JoshuaEgwuatu/Capstone-Spring2023-CitizenAirQualitySensor/Documentation/Electrical/Schematics/ReadMe.md

A collection of all the schematics that are related to and used for the design and its subsystems.  Schematics may be PDF or JPEG format.
