JoshuaEgwuatu/Capstone-Spring2023-CitizenAirQualitySensor/Reports/Presentations/LithiumIonBatteries.pdf

# Lithium Ion Batteries

By Kaleb Irwin
Team 1

# Why batteries?

The world needs compact energy storage

Devices need electricity when not plugged in

Can be used as power backups

# Advantages of Li+

High Energy density

Low self discharge (under half NiCd and NiMH)

Minimal memory effect

Longer lifespan than other common compositions

# Individual cells

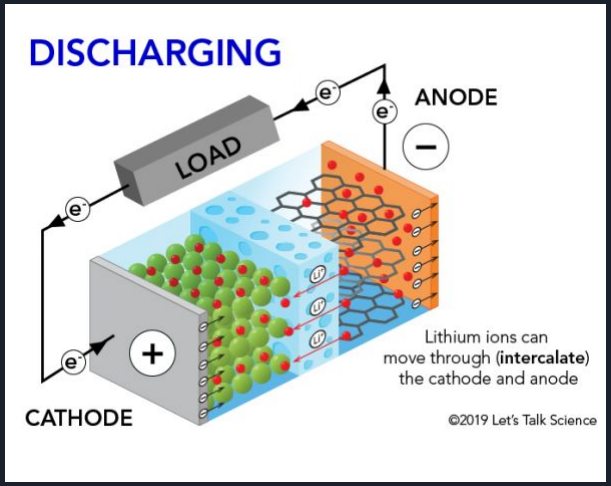
[picture p28: figure]

Consists of

- Cathode
- Anode
- Electrolyte

Materials for all of the components can be tweaked to alter the performance of the battery

# Cathode

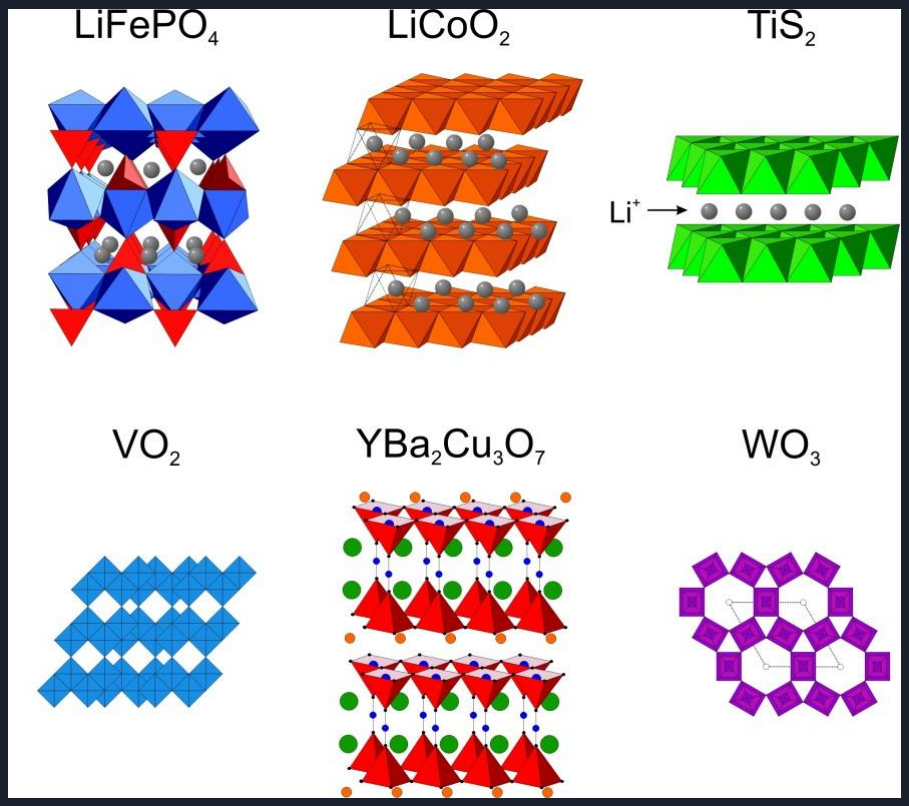
[picture p29: figure]

Positive Electrode

Household batteries mark the cathode with +

Typically a Metal Oxide Crystal with Lithium Metal inserted

Absorbs Electrons that are made by the battery

# Common Cathode Materials

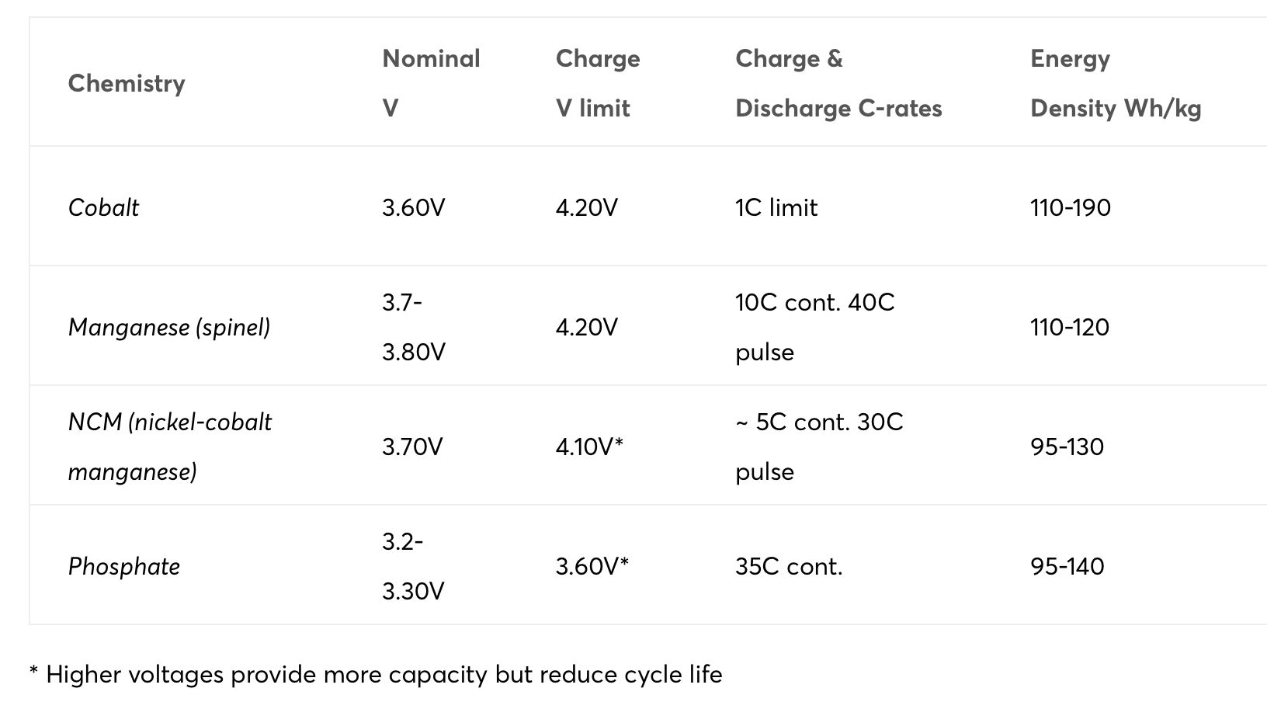
[picture p30: figure]

Different Cathode
materials can provide
- higher energy
densities
- higher current
output
- more charge
cycles

# Electrolyte

Chemical Separator

usually a lithium salt

Permeable for lithium ions but not electrons

Originally these were only permeable in one direction

Today they are bi-directional

# Common Electrolytes

Most common by far is Lithium Hexafluorophosphate

Other additives can be placed in solution with the salt to decrease the deposition rate or increase the reaction rate

Increasingly common is solid electrolytes that limit the degradation of the battery and are much safer.

# Anode

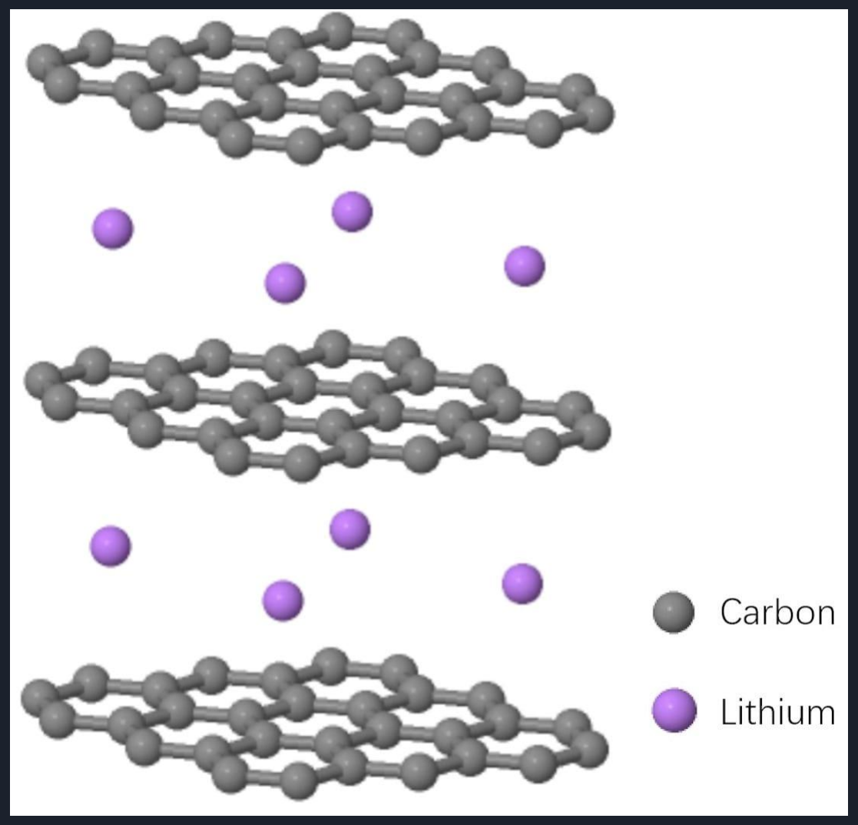
[picture p31: figure]

Negative Electrode

Emitter for the electrons generated

Almost always made of graphite due to its ability to place lithium ions between layers and its high conductivity

# Other Anodes

Graphite anodes require six carbon atoms per lithium ion

This is a waste of space and energy density

Silicon can be used as it binds to more lithium

- This is expensive and dangerous as it expands while discharging

Usually silicon is added to the graphite as an impurity of around 3% to increase energy density

Also use lithium titanate to decrease charge time

# Electrochemistry

Two reactions happen

The first one is a reaction at the anode

This generates an electron and a positively charged lithium ion and releases the chemical potential as electrical potential

# Electrochemistry

The second reaction happens at the cathode

The metal oxide and lithium ion react with the electron and form the multi metal oxide

# Electrochemistry

The reaction rate at the cathode is determined by the availability of electrons

Larger resistances in the external circuit that connects the cathode and anode limit how many electrons flow to the cathode

This means the discharge rate is determined by the resistance of the external circuit

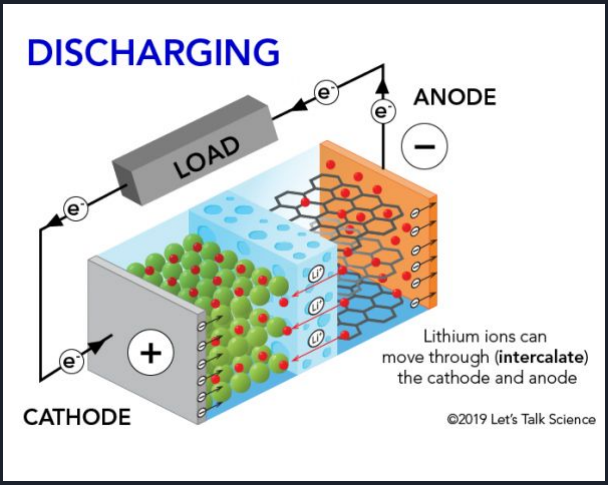
[picture p32: figure]

# What determines Voltage?

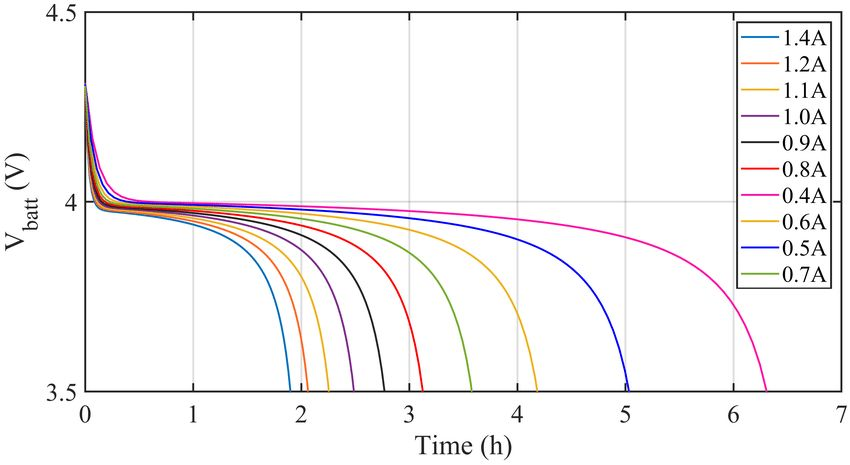
[picture p33: figure]

The voltage is intrinsic to the reaction and is based on the compounds used.

The voltage is slightly dependant on concentration

Because of this the voltage can change as the battery is
discharged

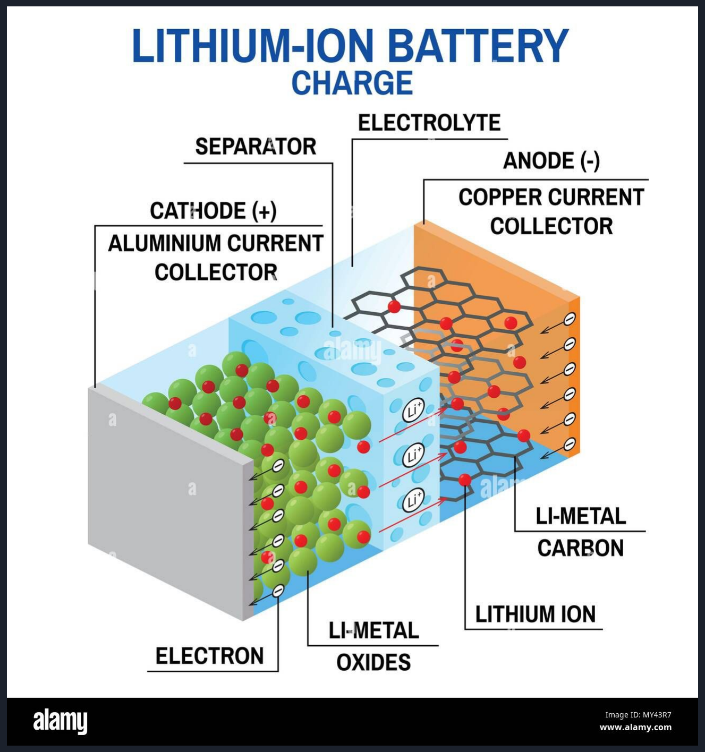
[picture p34: figure]

# Charging

A higher voltage than the
discharge voltage is applied

This supplies enough energy to cause the reactions to reverse

The electrons then leave the metal oxide and return to the graphite sheets

# Format of cells

Putting two cells in series will cause their voltages to add

Putting two cells in parallel will cause their capacities to add

Commonly abbreviated with S and P

Ex. 4s2p

Allows operation at higher voltages and load requirements

More efficient than one big battery

# Charging Multi-Celled batteries

Requires 3 steps

Constant current charging

Voltage balancing so all the cells are the same voltage

Constant Voltage charging

# Lifetime performance

Lifetime of the battery is determined by

- Temperature of the battery
- Reaction is exothermic so it heats the battery
- Reaction is 100% reversible
- Some of the lithium is deposited on the electrodes and is lost
- Charge and discharge current
- Increasing these also increases the rate of deposition

# References

https://www.energy.gov/science/doe-explainsbatteries

https://batteryuniversity.com/article/bu-204-how-do-lithium-batteries-work

https://www.targray.com/li-ion-battery/cathode-materials

https://en.wikipedia.org/wiki/Lithium-ion_battery
