JoshuaEgwuatu/Capstone-Spring2023-CitizenAirQualitySensor/Documentation/ProjectPhotos/Box1Exterior1.pdf

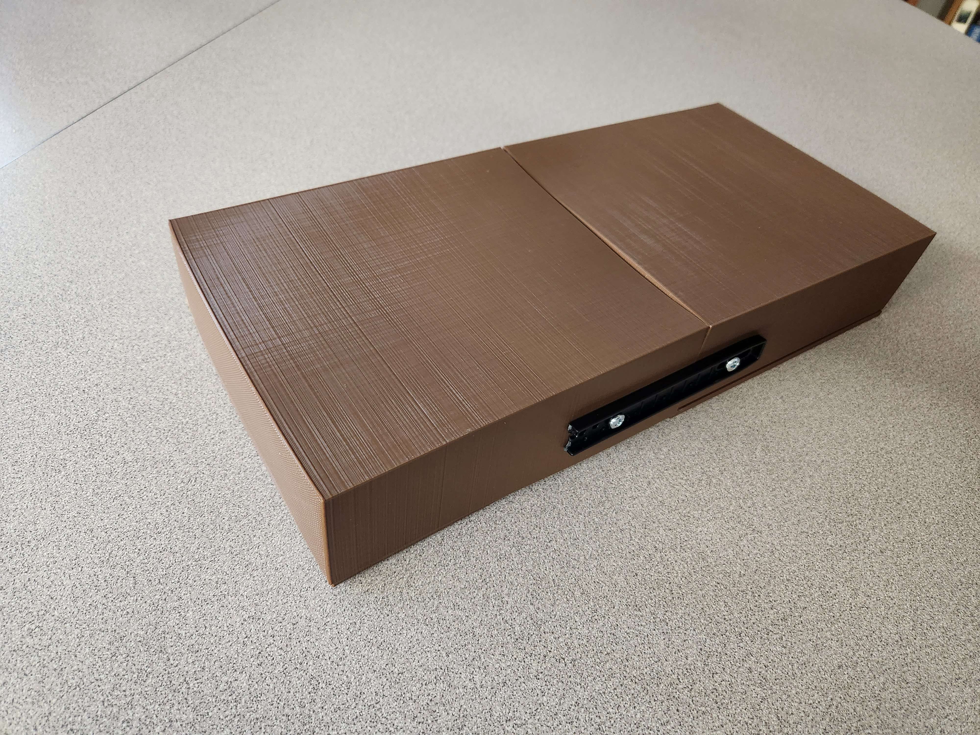
[picture p41: page 1]
