JoshuaEgwuatu/Capstone-Spring2023-CitizenAirQualitySensor/Documentation/ProjectPhotos/Box1Exterior2.pdf

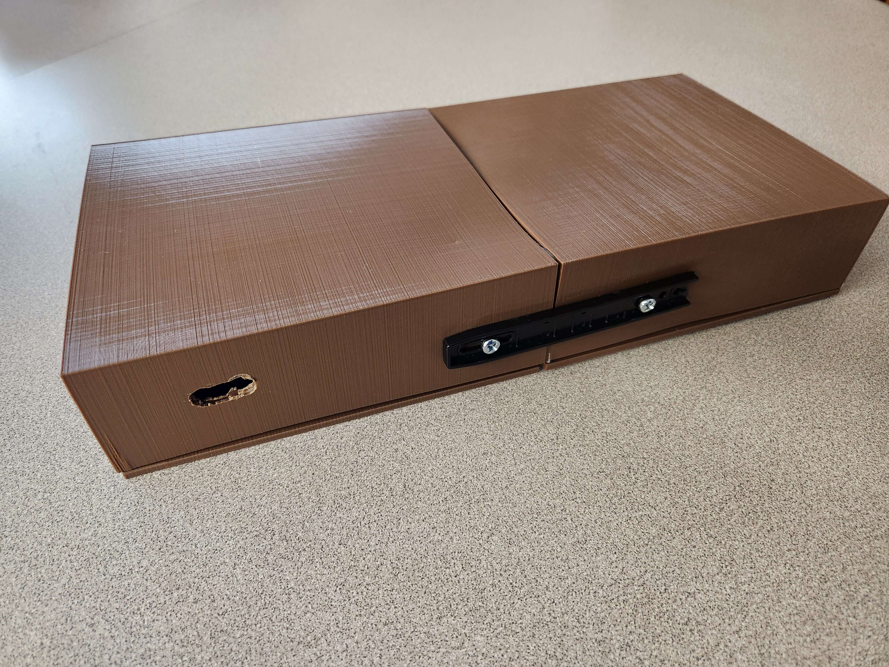
[picture p42: page 1]
