JoshuaEgwuatu/Capstone-Spring2023-CitizenAirQualitySensor/Documentation/ProjectPhotos/Box1Interior.pdf

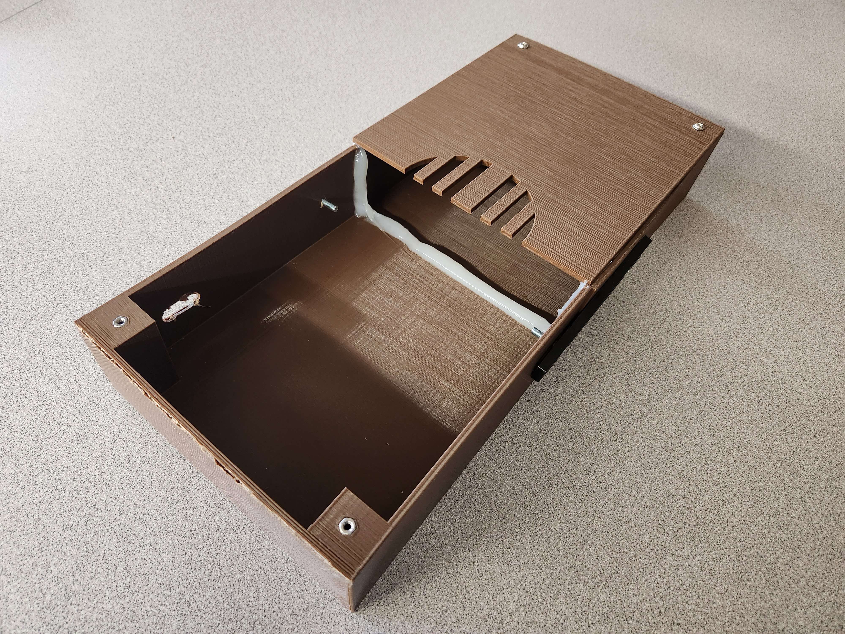
[picture p43: page 1]
