JoshuaEgwuatu/Capstone-Spring2023-CitizenAirQualitySensor/Documentation/ProjectPhotos/Box1Vent.pdf

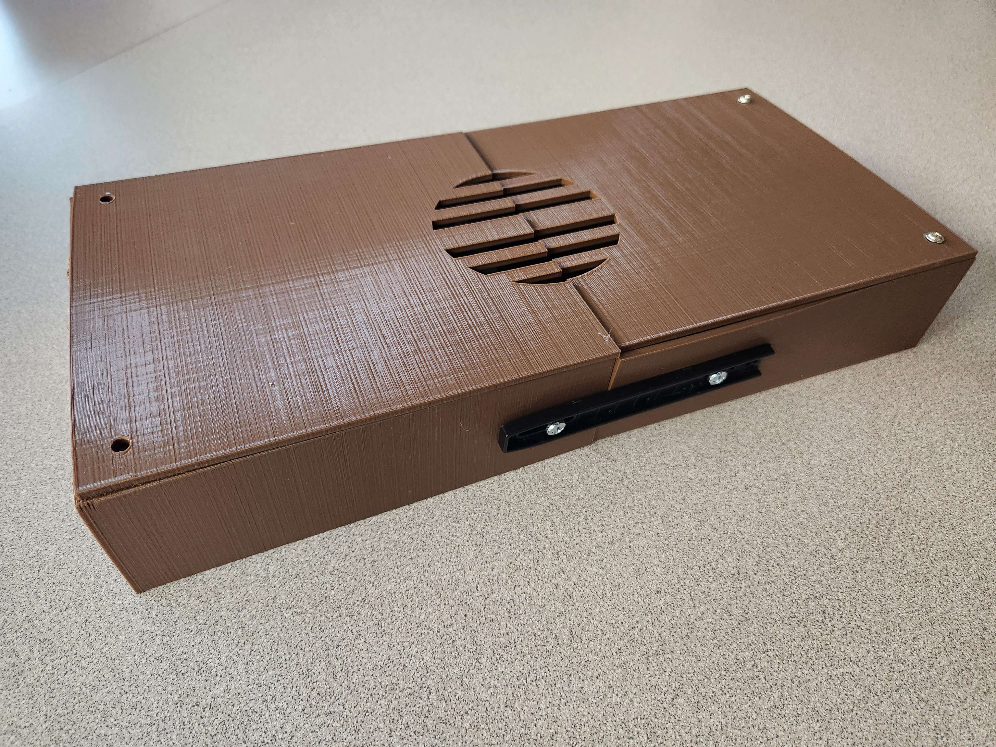
[picture p44: page 1]
