JoshuaEgwuatu/Capstone-Spring2023-CitizenAirQualitySensor/Documentation/ProjectPhotos/Box2Exterior.pdf

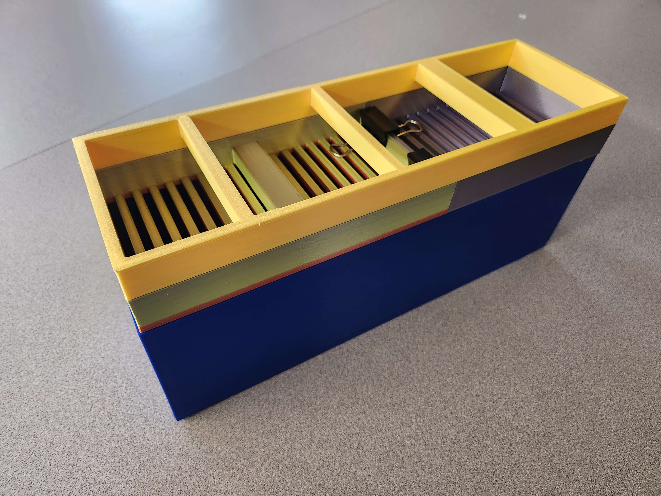
[picture p45: page 1]
