JoshuaEgwuatu/Capstone-Spring2023-CitizenAirQualitySensor/Documentation/ProjectPhotos/GUTS1.pdf

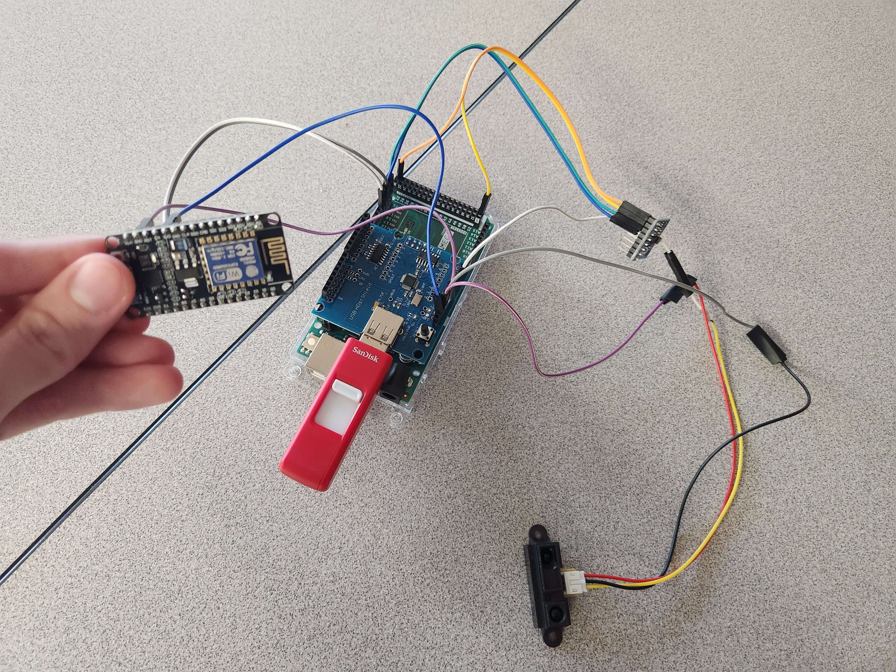
[picture p48: page 1]
