JoshuaEgwuatu/Capstone-Spring2023-CitizenAirQualitySensor/Documentation/ProjectPhotos/GUTS2.pdf

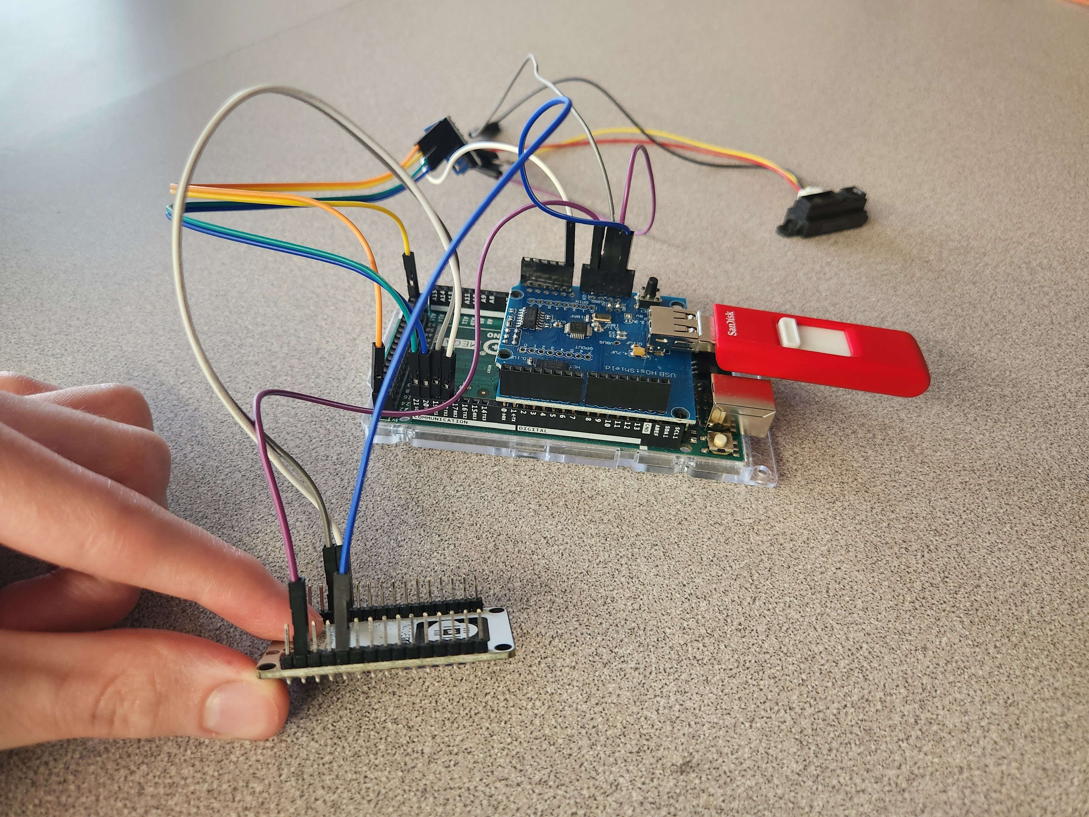
[picture p49: page 1]
