JoshuaEgwuatu/Capstone-Spring2023-CitizenAirQualitySensor/Documentation/ProjectPhotos/GUTS3.pdf

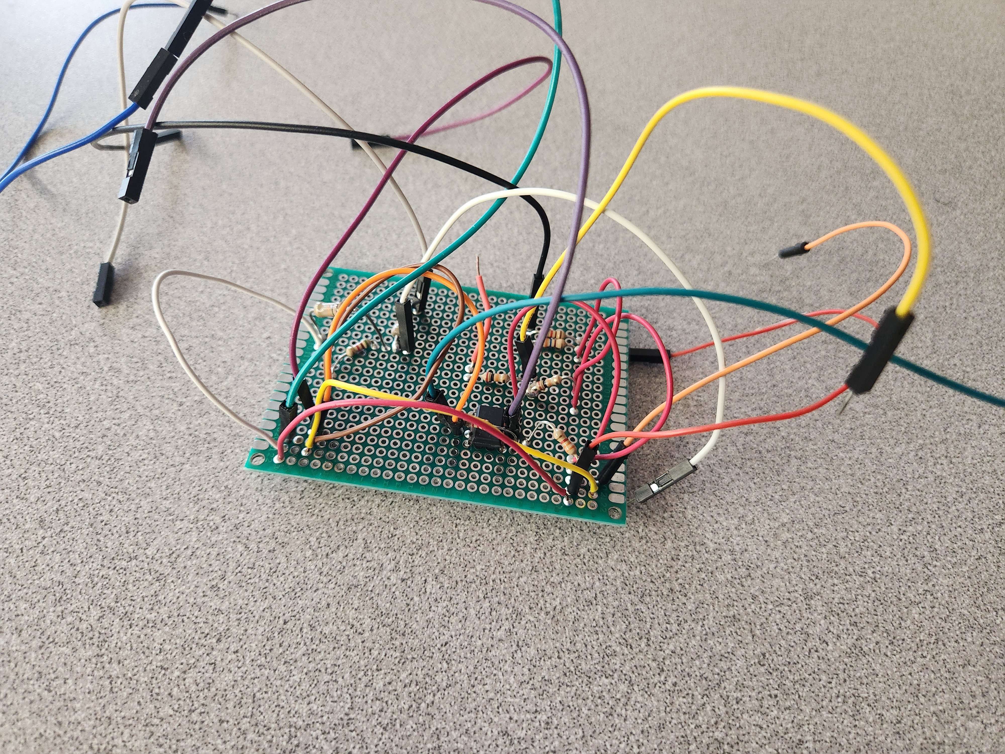
[picture p50: page 1]
