JoshuaEgwuatu/Capstone-Spring2023-CitizenAirQualitySensor/Documentation/Images/CAPSTONE Team 1 Timeline.png

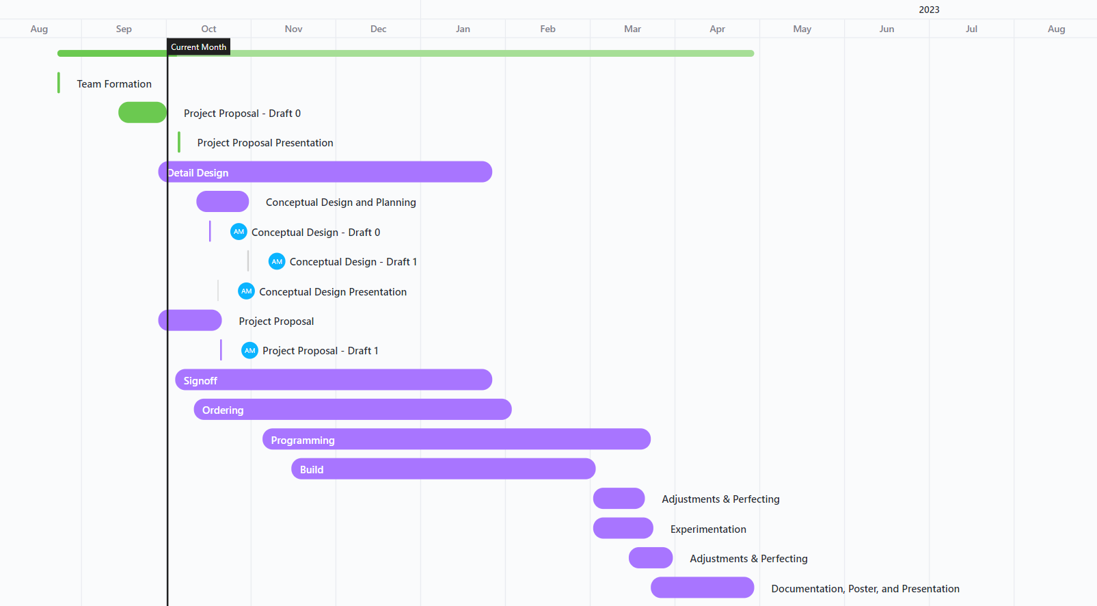
Documentation/Images/CAPSTONE Team 1 Timeline.png
