JoshuaEgwuatu/Capstone-Spring2023-CitizenAirQualitySensor/Documentation/Images/Psuedo-code_Comm2.jpg

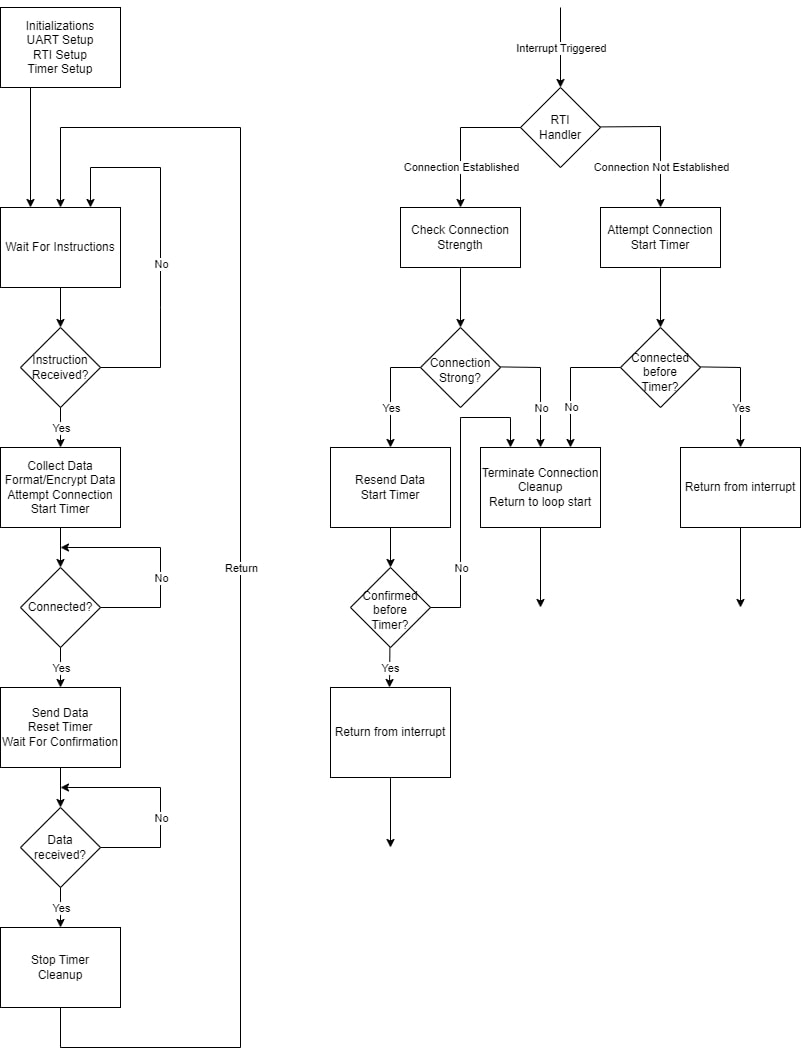
Documentation/Images/Psuedo-code_Comm2.jpg
