JoshuaEgwuatu/Capstone-Spring2023-CitizenAirQualitySensor/Documentation/Images/Psuedo-code_Comm.JPG

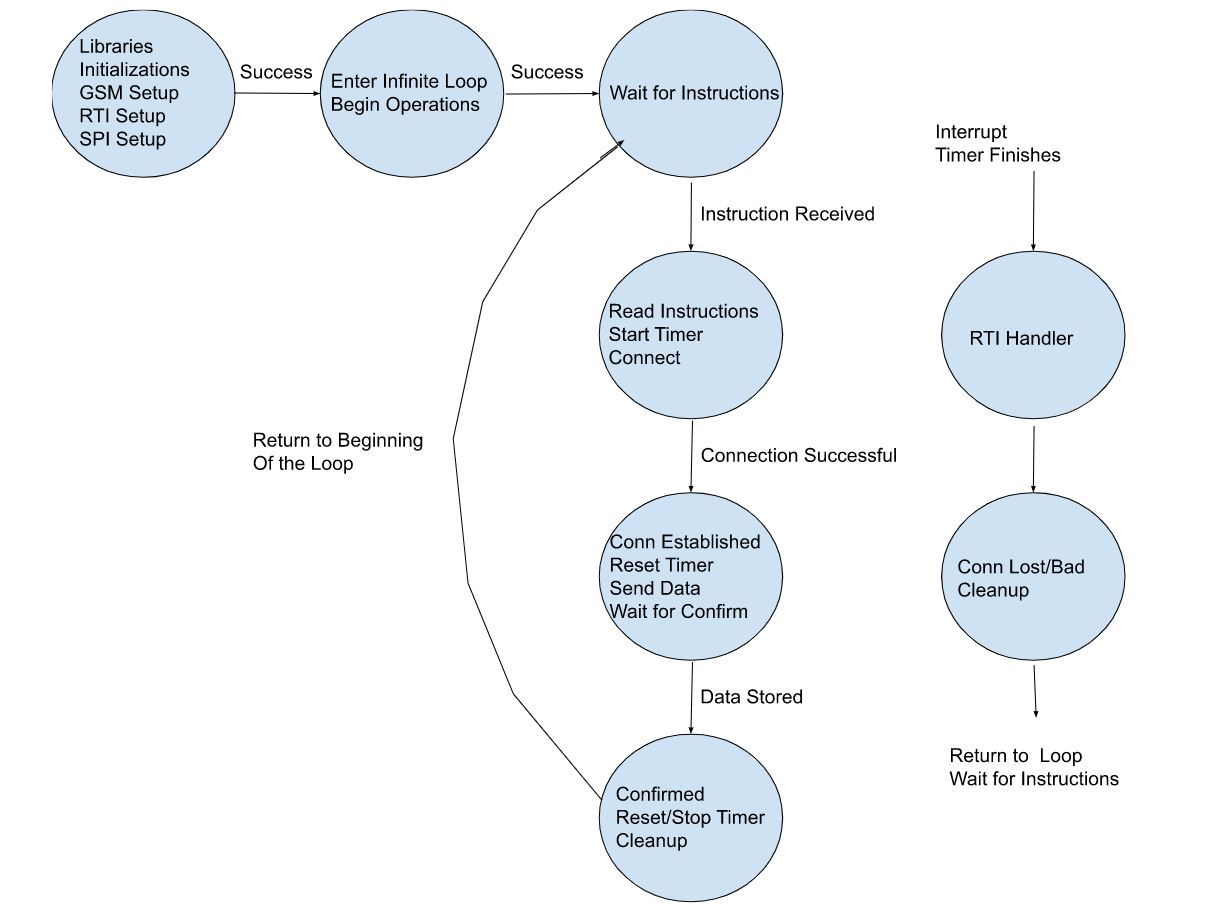
Documentation/Images/Psuedo-code_Comm.JPG
